gabemorris12/Servo-Laser/SolidWorks/Laser Mount/Laser Couple Top.SLDPRT

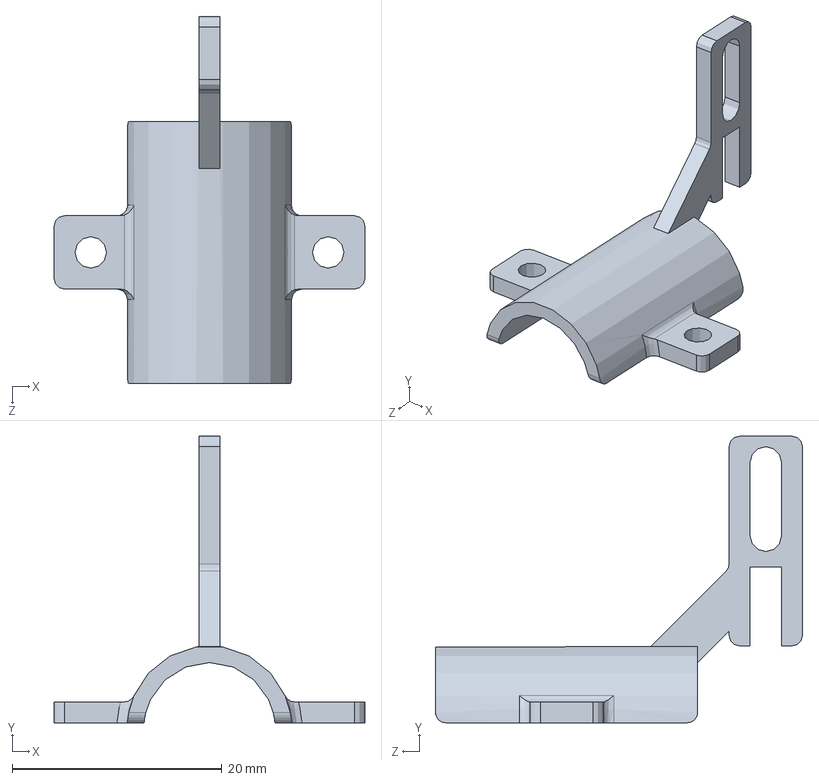
[picture p20: CAD file, 2021-08-11]
SolidWorks/Laser Mount/Laser Couple Top.SLDPRT
29.6 x 27.3 x 35.0 mm
