gabemorris12/Servo-Laser/SolidWorks/Tensioner Assembly/Center Female.SLDPRT

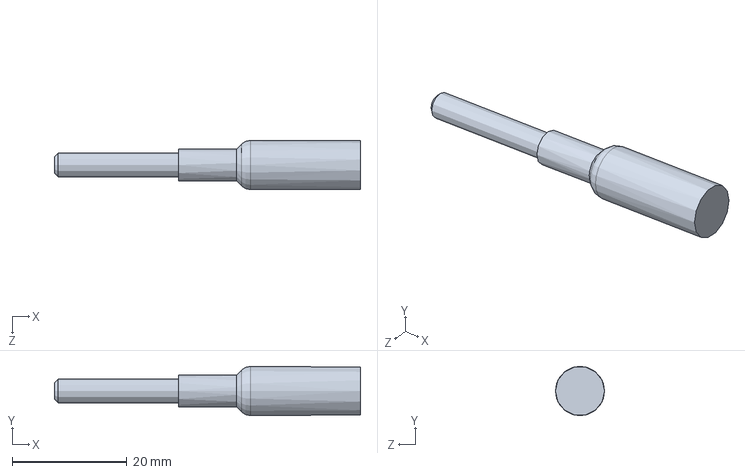
[picture p21: CAD file, 2021-08-03]
SolidWorks/Tensioner Assembly/Center Female.SLDPRT
53.3 x 8.57 x 8.57 mm
