gabemorris12/Servo-Laser/SolidWorks/Laser Mount/Switch.SLDPRT

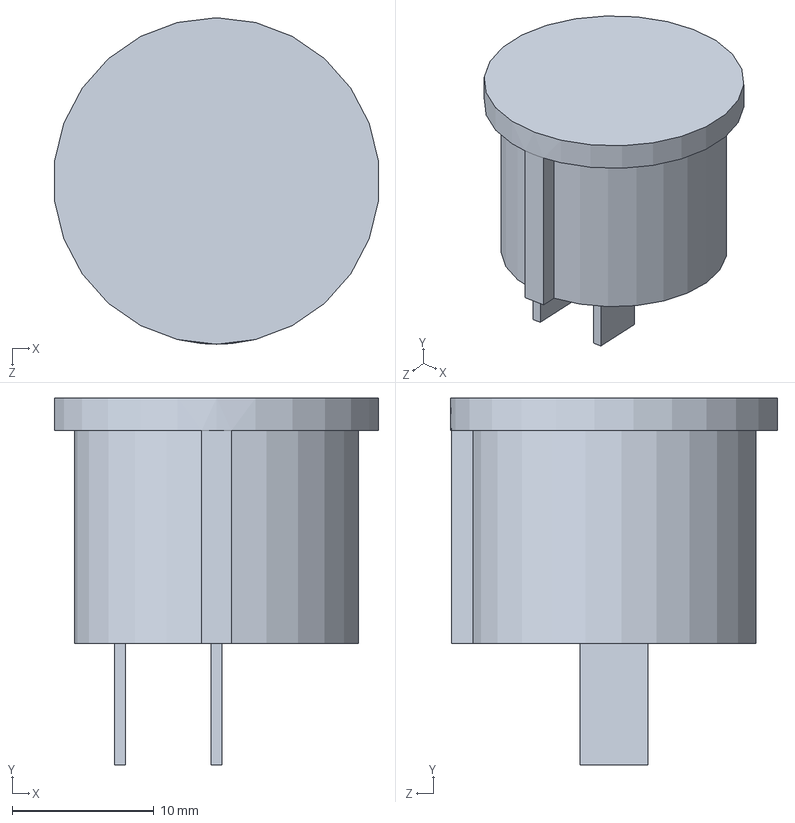
[picture p22: CAD file, 2021-08-11]
SolidWorks/Laser Mount/Switch.SLDPRT
22.8 x 25.9 x 23.0 mm
