gabemorris12/Servo-Laser/SolidWorks/Tensioner Assembly/Tensioner Inner.SLDPRT

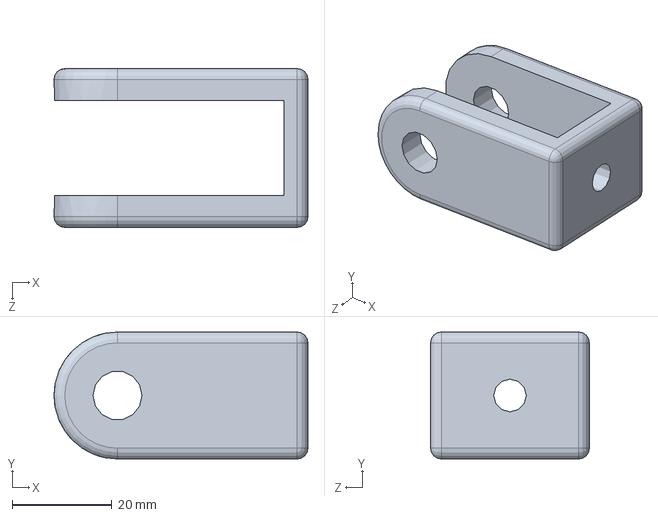
[picture p23: CAD file, 2021-08-03]
SolidWorks/Tensioner Assembly/Tensioner Inner.SLDPRT
50.8 x 25.4 x 31.8 mm
