gabemorris12/Servo-Laser/SolidWorks/Laser Mount/Laser Couple Bottom.SLDPRT

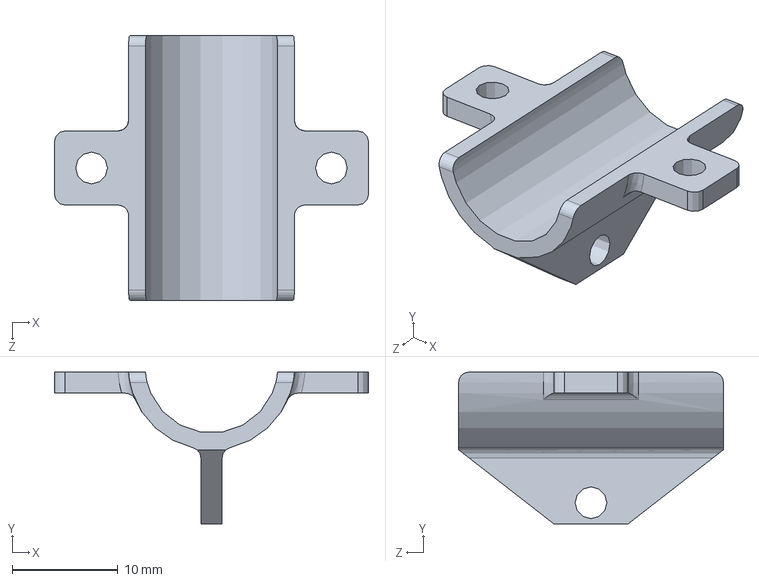
[picture p24: CAD file, 2021-08-11]
SolidWorks/Laser Mount/Laser Couple Bottom.SLDPRT
29.6 x 14.3 x 25.0 mm
