gabemorris12/Servo-Laser/SolidWorks/Tensioner Assembly/Center Male.SLDPRT

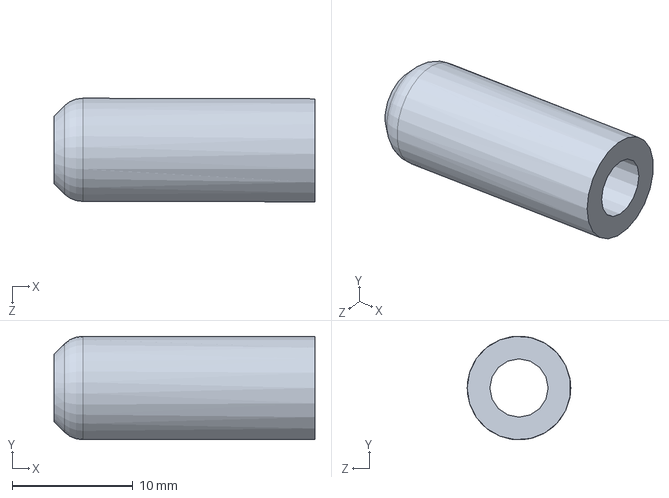
[picture p25: CAD file, 2021-08-03]
SolidWorks/Tensioner Assembly/Center Male.SLDPRT
21.6 x 8.56 x 8.57 mm
